jgpeiro/black_scope/images/capture engine 2.png

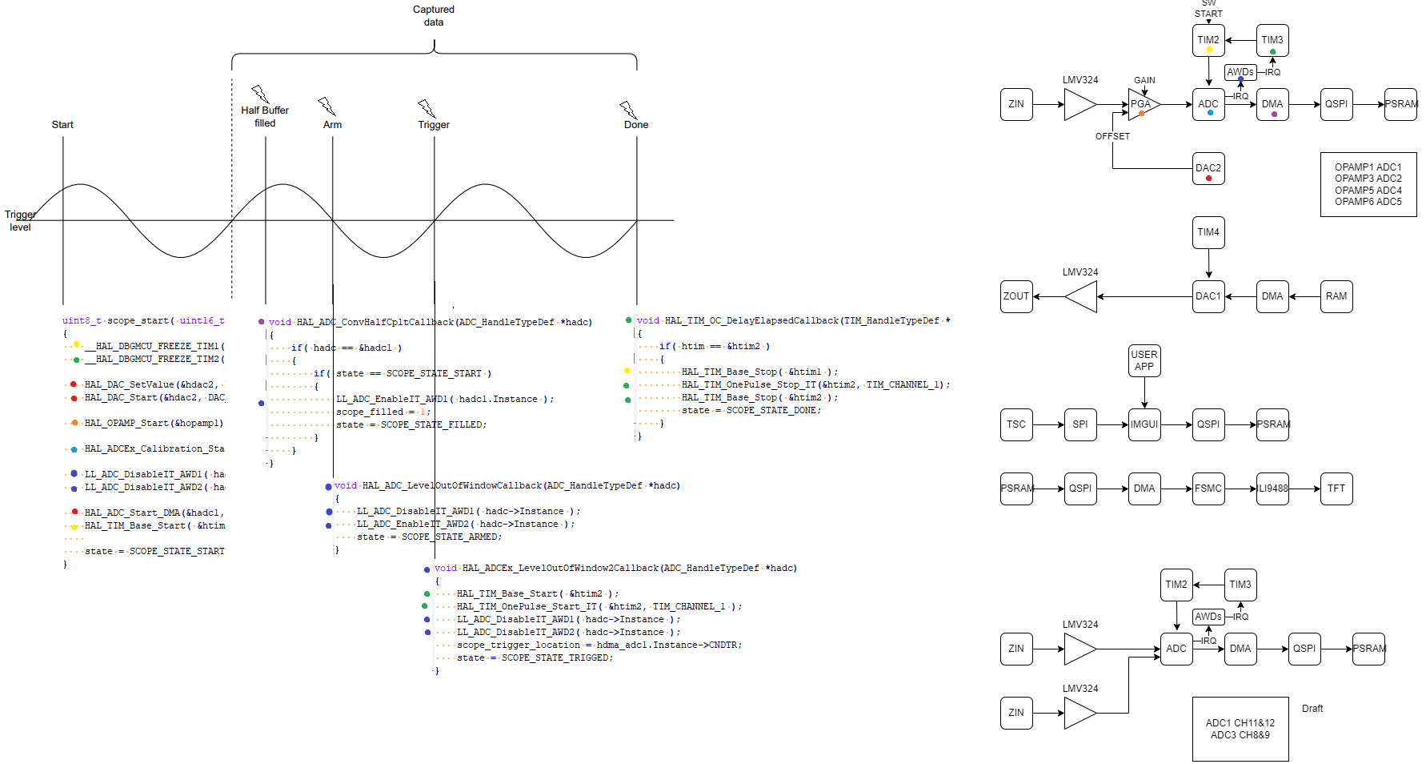
images/capture engine 2.png
