jgpeiro/black_scope/images/microui.jpg

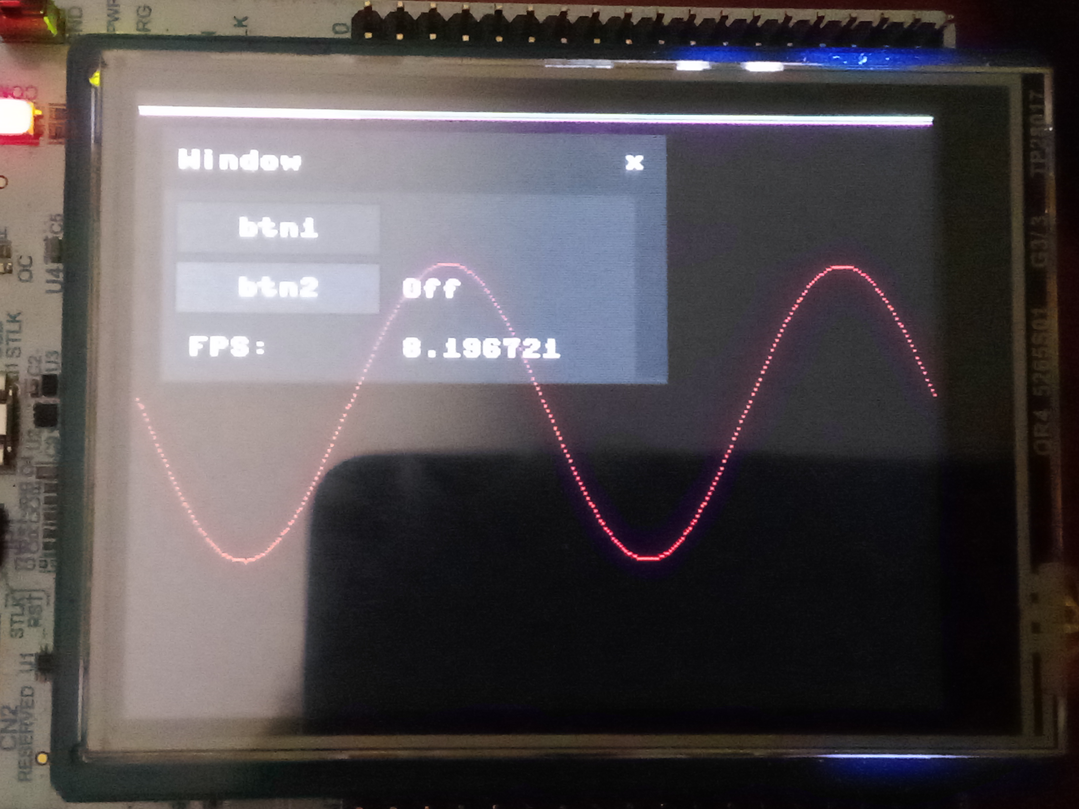
images/microui.jpg
