jgpeiro/black_scope/images/pcb detail.png

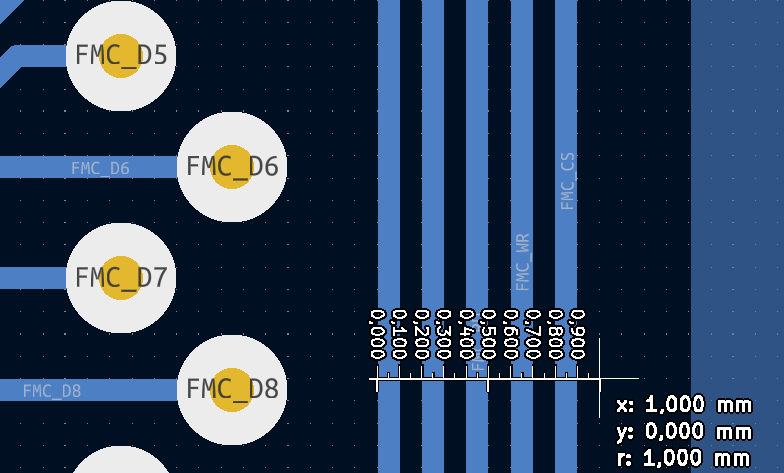
images/pcb detail.png
