jgpeiro/black_scope/images/Photo-2.jpeg

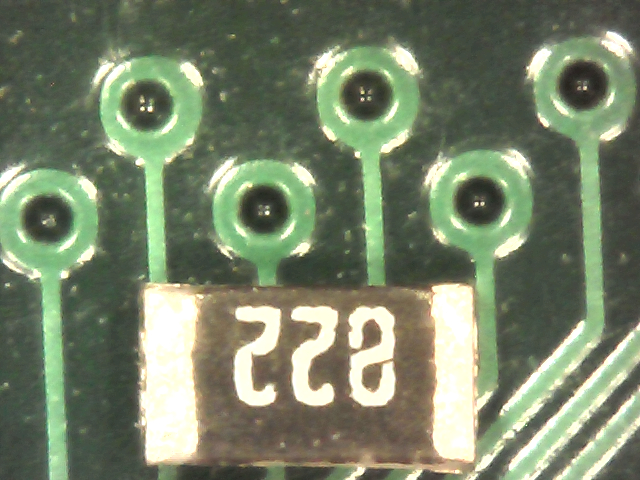
images/Photo-2.jpeg
