jgpeiro/black_scope/images/Photo-3.jpeg

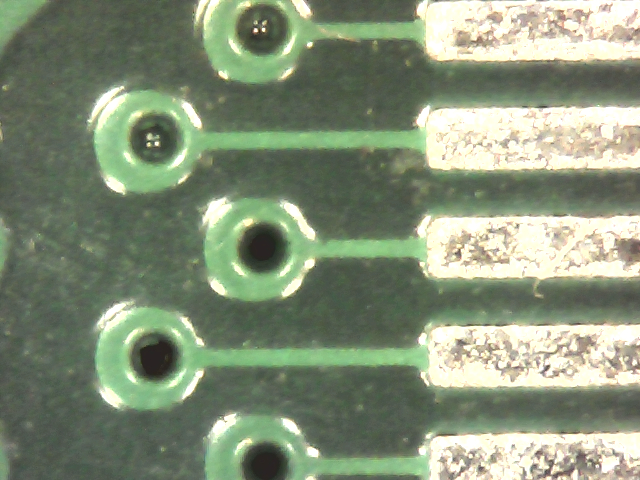
images/Photo-3.jpeg
