jgpeiro/black_scope/images/Photo-4.jpeg

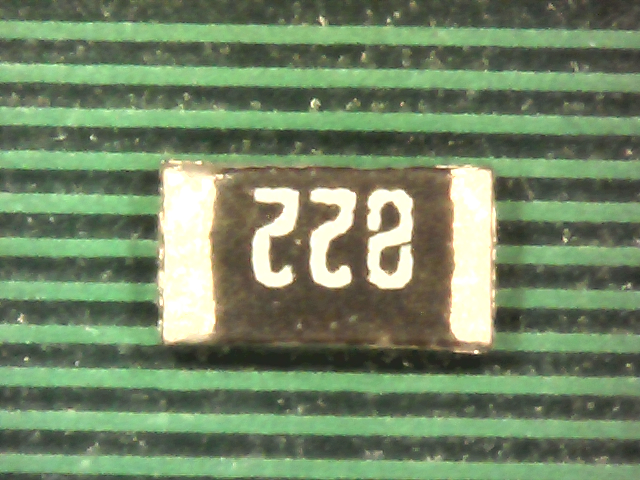
images/Photo-4.jpeg
