jgpeiro/black_scope/images/Untitled Diagram.drawio.png

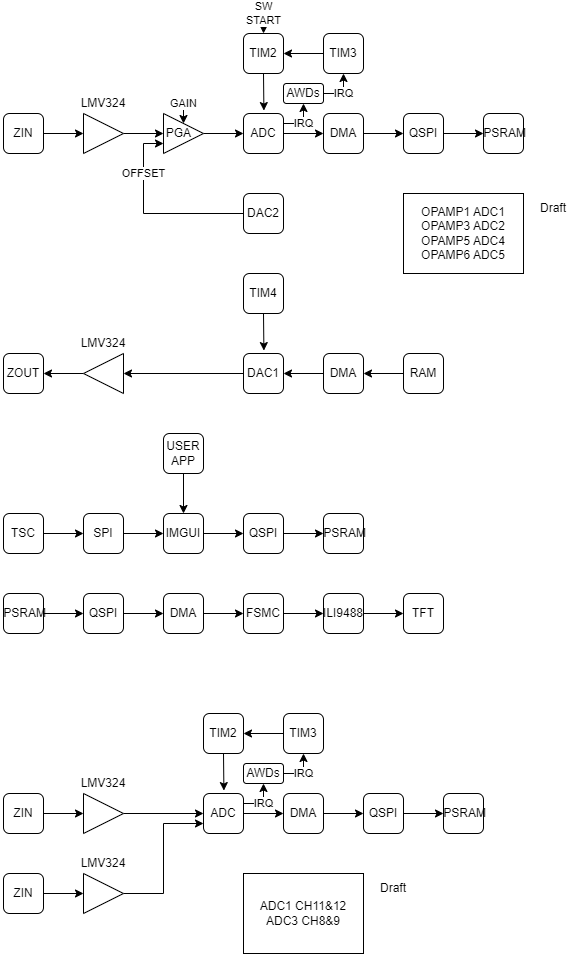
images/Untitled Diagram.drawio.png
