jgpeiro/black_scope/images/pcb_back_3d_print.jpg

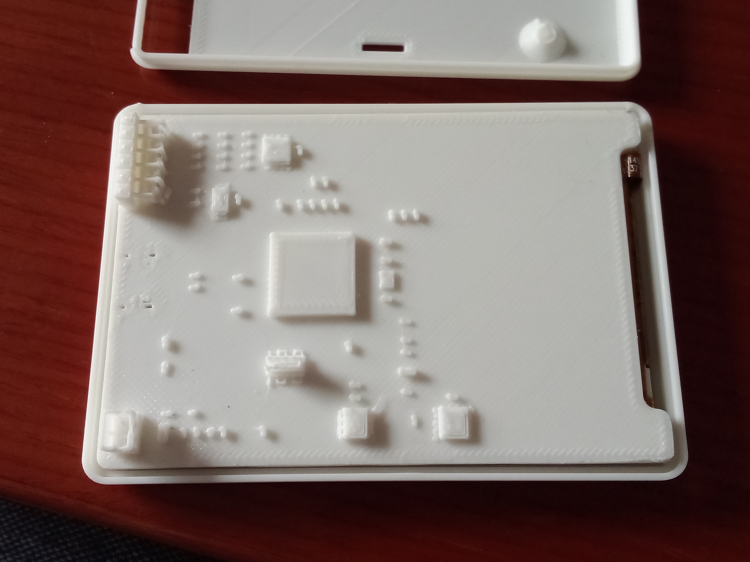
images/pcb_back_3d_print.jpg
